jliniesta/G4_ELCO_2020-21/Diseño final/Diseño mecanico/2relojes.png

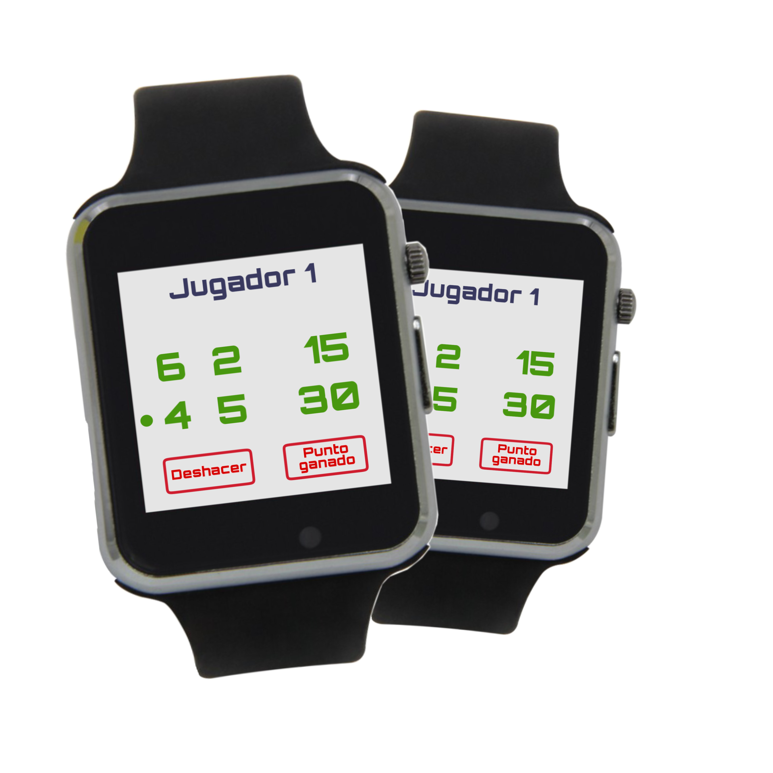
Diseño final/Diseño mecanico/2relojes.png
