jliniesta/G4_ELCO_2020-21/Prototipo/Esquematicos/esquematicos_reloj.png

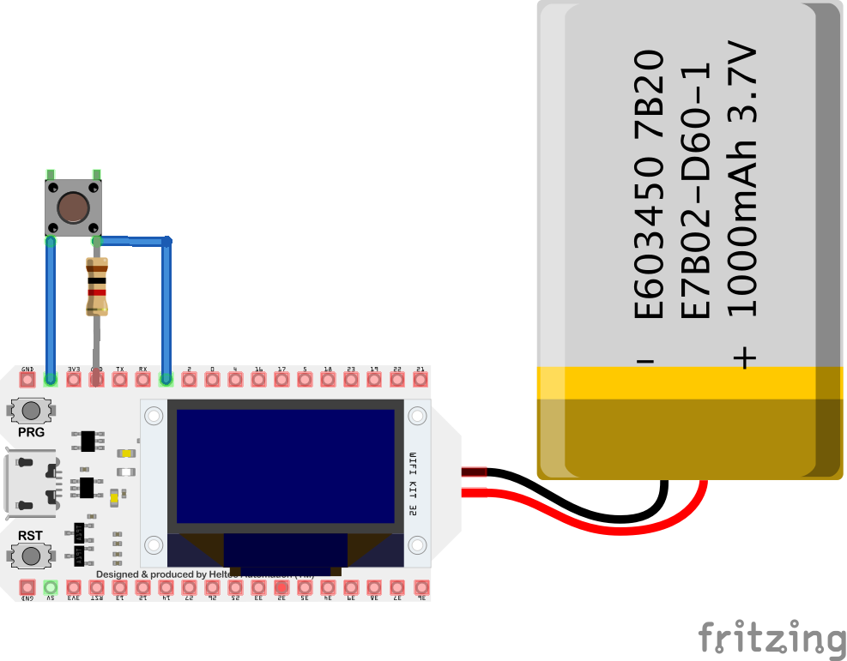
Prototipo/Esquematicos/esquematicos_reloj.png
