jliniesta/G4_ELCO_2020-21/Prototipo/Resultado final prototipo/marcador.jpg

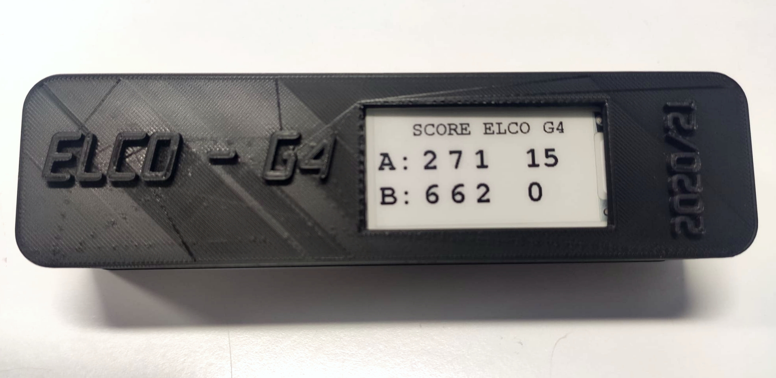
Prototipo/Resultado final prototipo/marcador.jpg
