jliniesta/G4_ELCO_2020-21/Prototipo/Resultado final prototipo/resultado_final_prototipo.jpg

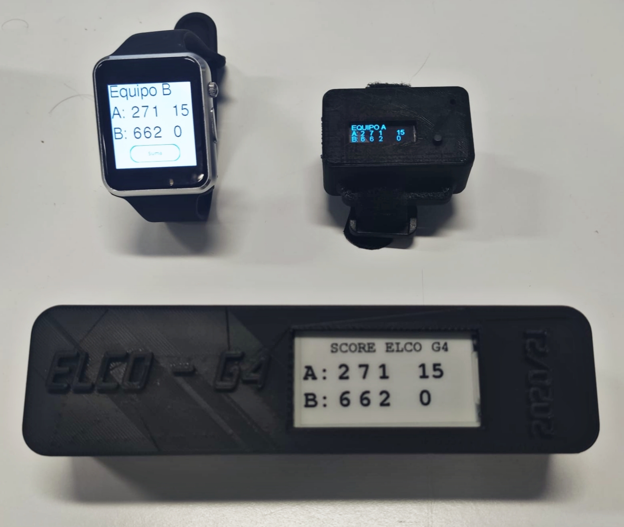
Prototipo/Resultado final prototipo/resultado_final_prototipo.jpg
